yukke1117/pj-bis2025-kicad/step/OPA2380AIDGKR.stp

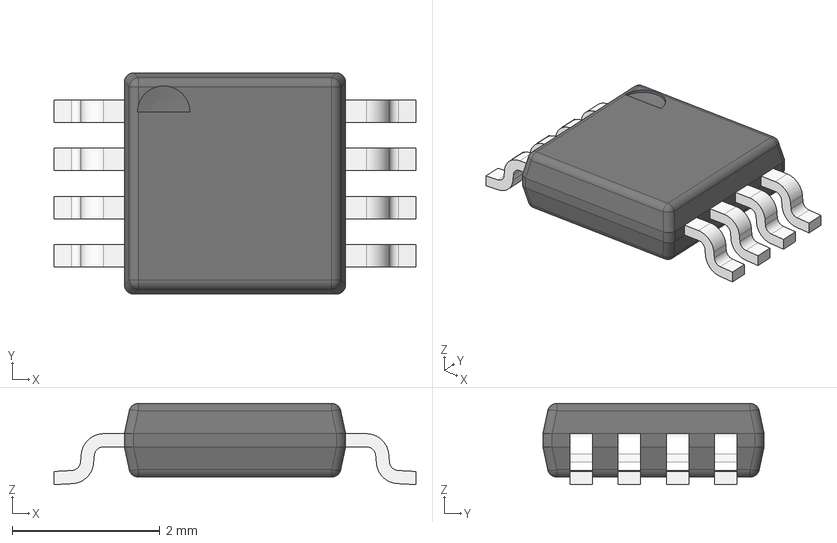
[picture p15: CAD file, 2026-01-05]
step/OPA2380AIDGKR.stp
4.90 x 3.00 x 1.10 mm
BODY_MUA08A
LEAD_MUA08A x 8
