yukke1117/pj-bis2025-kicad/step/REF5050IDR.stp

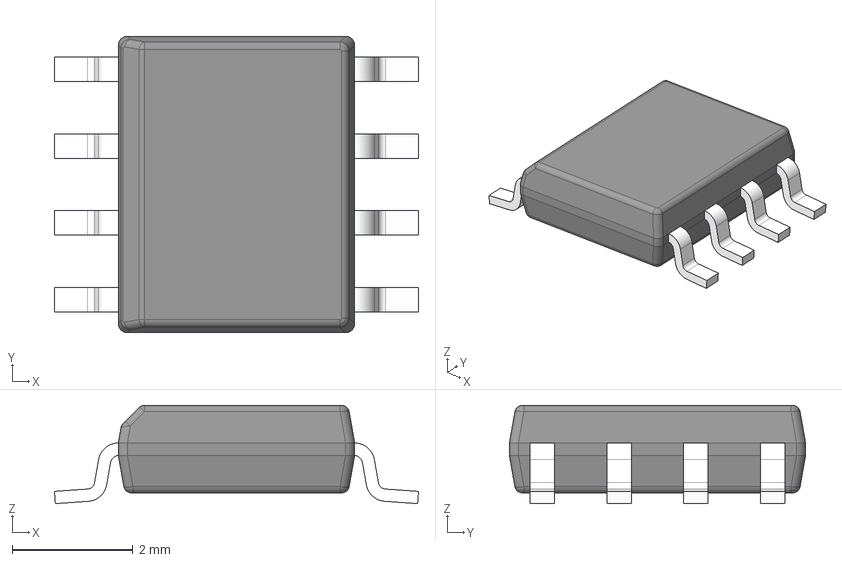
[picture p16: CAD file, 2026-01-05]
step/REF5050IDR.stp
6.02 x 4.90 x 1.63 mm
BODY-SO
LEAD-D0008A x 8
