yukke1117/pj-bis2025-kicad/step/ALD114904APAL.step

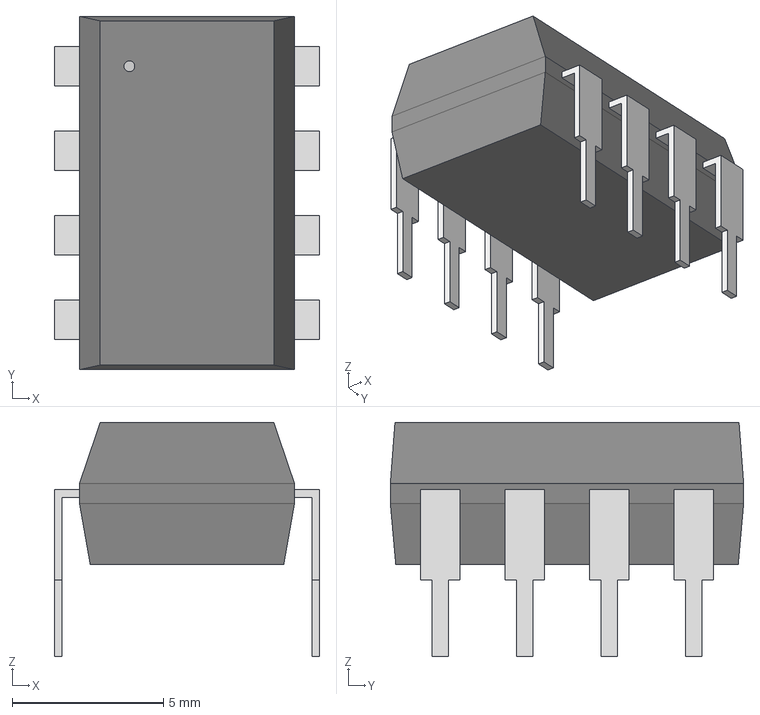
[picture p17: CAD file, 2026-01-05]
step/ALD114904APAL.step
8.76 x 11.7 x 7.75 mm
